mandymadongyi/CASA0016-Individual-Prototype/Enclousure/Screenshot 2021-12-14 at 00.12.00.png

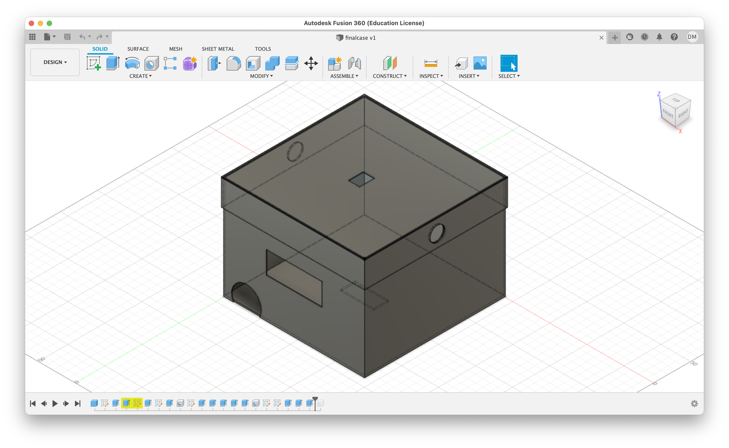
Enclousure/Screenshot 2021-12-14 at 00.12.00.png
