mandymadongyi/CASA0016-Individual-Prototype/Pictures/Figure 1. PH and mV mapping.jpg

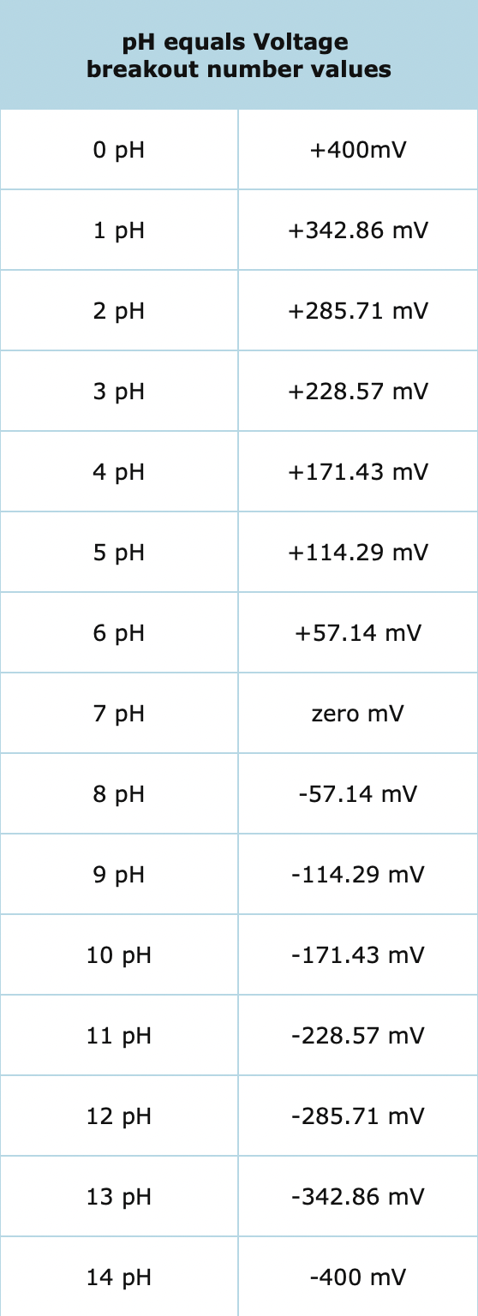
Pictures/Figure 1. PH and mV mapping.jpg
