mandymadongyi/CASA0016-Individual-Prototype/Pictures/Figure 4. PCB board circuit for PH sensor.JPG

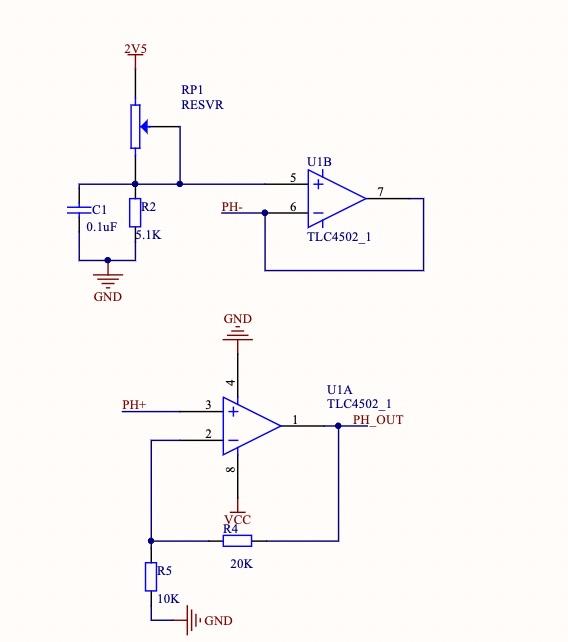
Pictures/Figure 4. PCB board circuit for PH sensor.JPG
