mandymadongyi/CASA0016-Individual-Prototype/Pictures/Figure 7. Fitting equation and line graph of the linear relation between PH and voltage.jpg

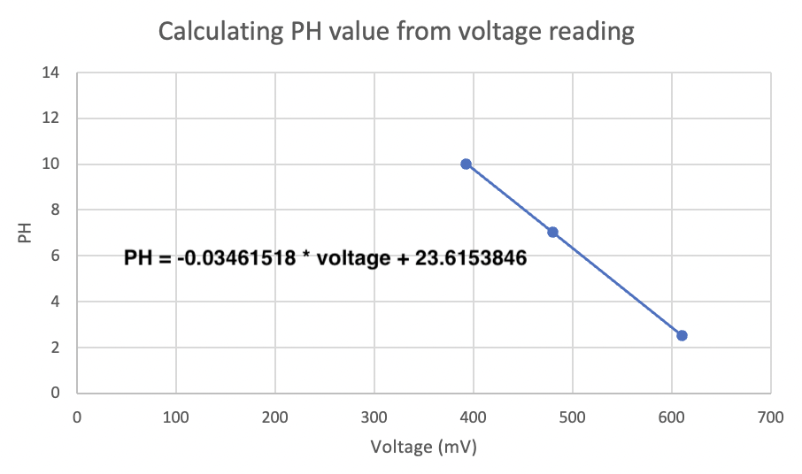
Pictures/Figure 7. Fitting equation and line graph of the linear relation between PH and voltage.jpg
