mandymadongyi/CASA0016-Individual-Prototype/Pictures/Figure 9. Connecting and Sending data to MQTT.jpg

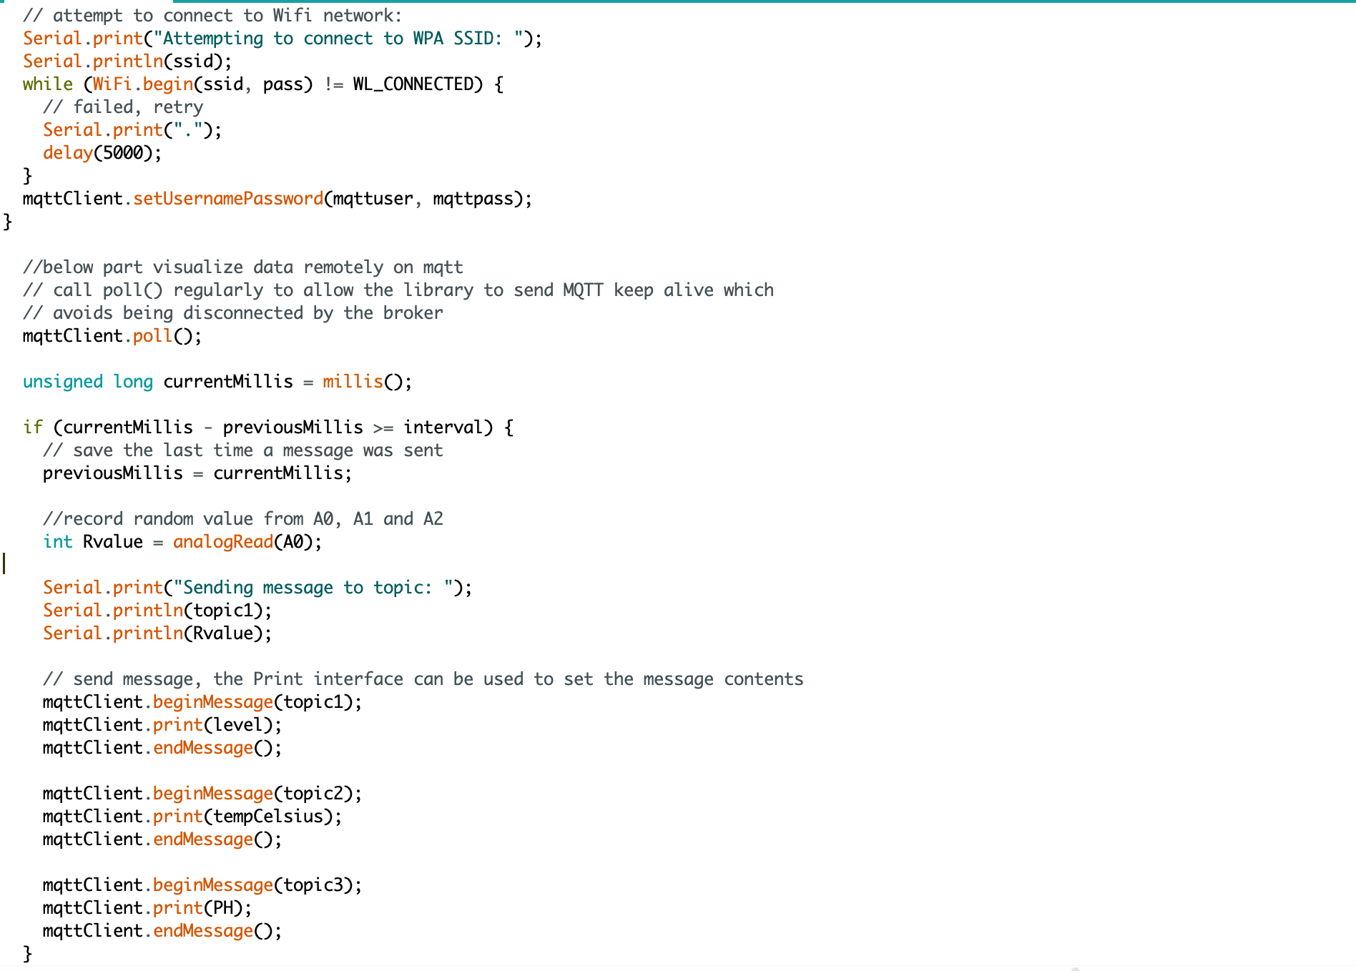
Pictures/Figure 9. Connecting and Sending data to MQTT.jpg
