mandymadongyi/CASA0016-Individual-Prototype/Pictures/Figure 10. Telegraf configuration.png

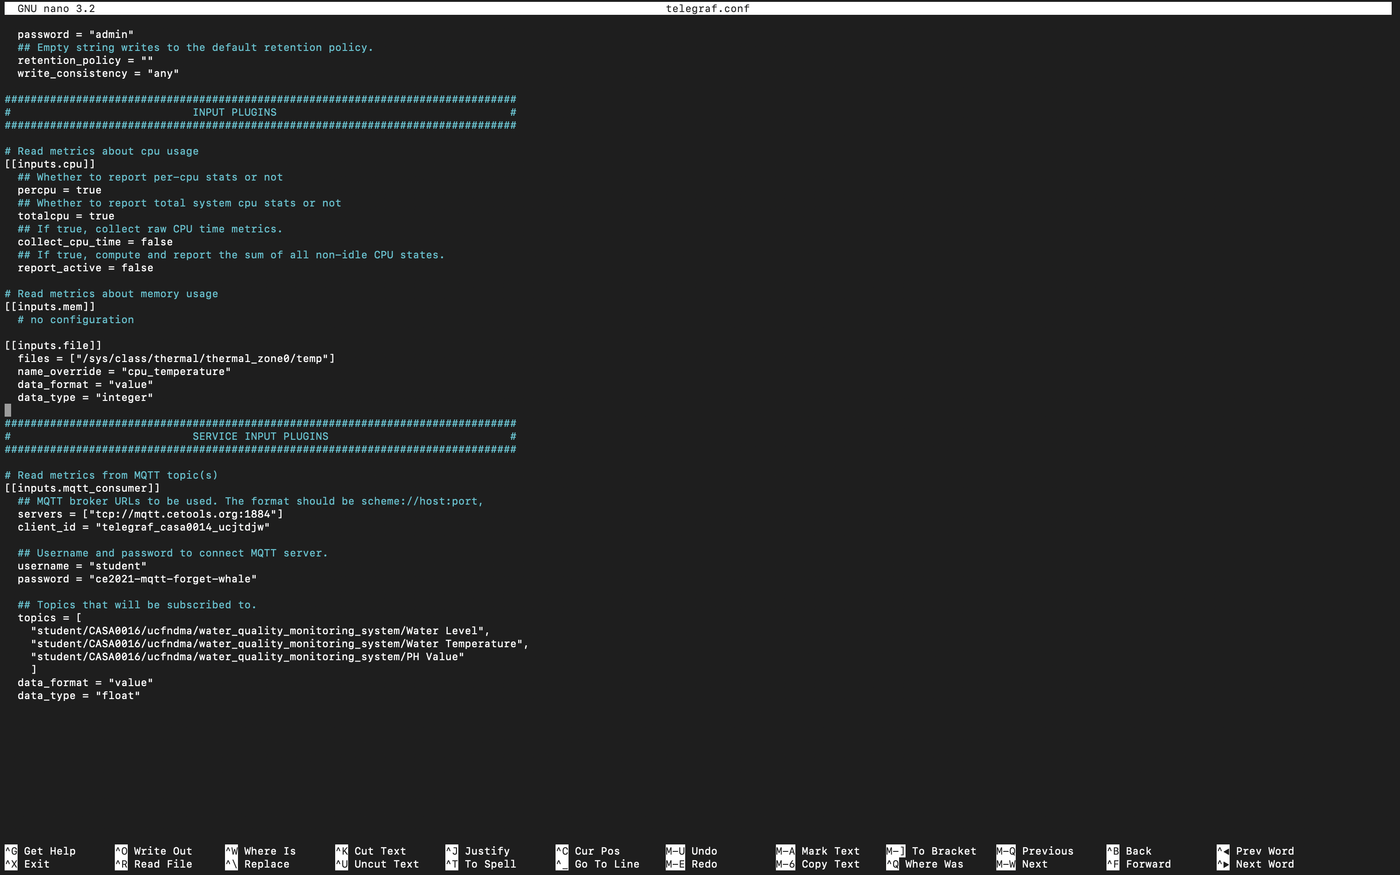
Pictures/Figure 10. Telegraf configuration.png
