mandymadongyi/CASA0016-Individual-Prototype/Pictures/Figure 13. Final prototype.jpg

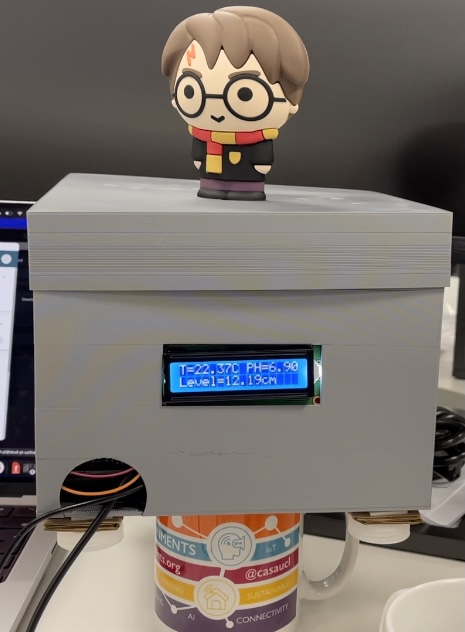
Pictures/Figure 13. Final prototype.jpg
