mandymadongyi/CASA0016-Individual-Prototype/Pictures/mqtt.JPG

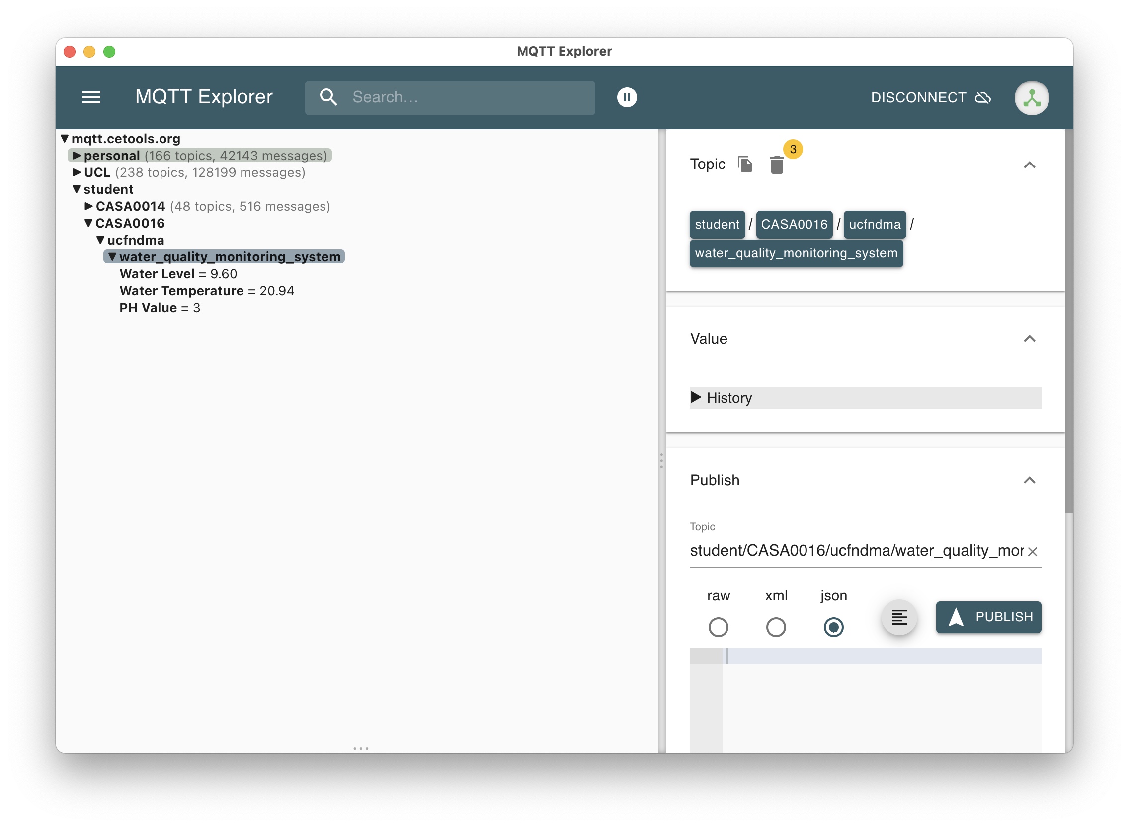
Pictures/mqtt.JPG
