mandymadongyi/CASA0016-Individual-Prototype/Pictures/Figure 8. Calculating water level and temperature, PH value and print on LCD.jpg

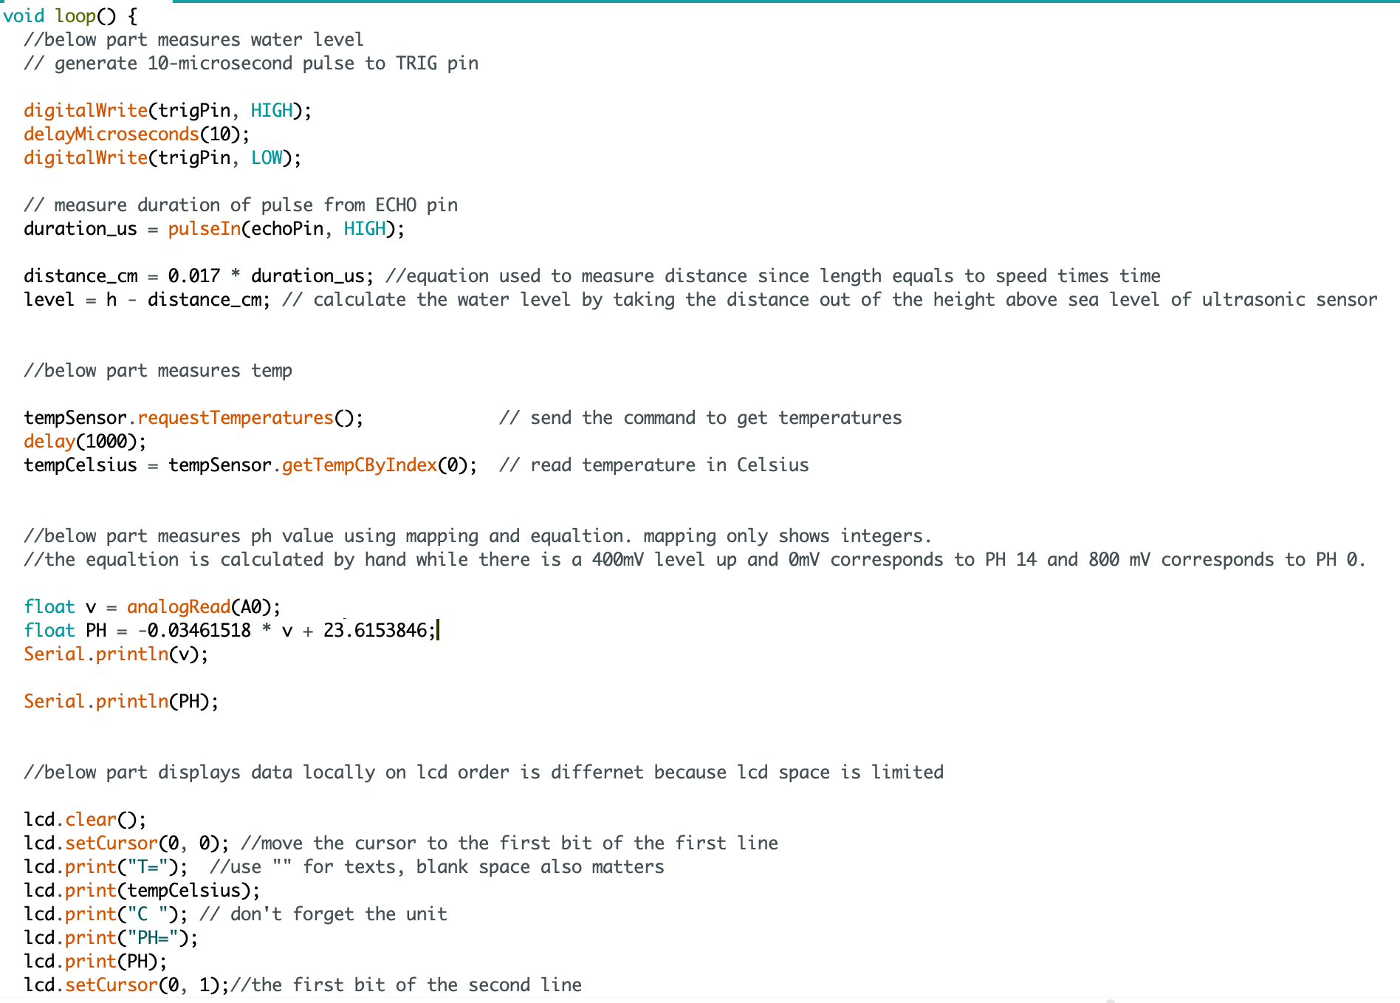
Pictures/Figure 8. Calculating water level and temperature, PH value and print on LCD.jpg
